HumanoidPequi/HumanoidPMec_LARC2023/Simulação/Martha_ws/src/martha_gazebo/src/worlds/robocup09_spl_field/thumbnails/4.png

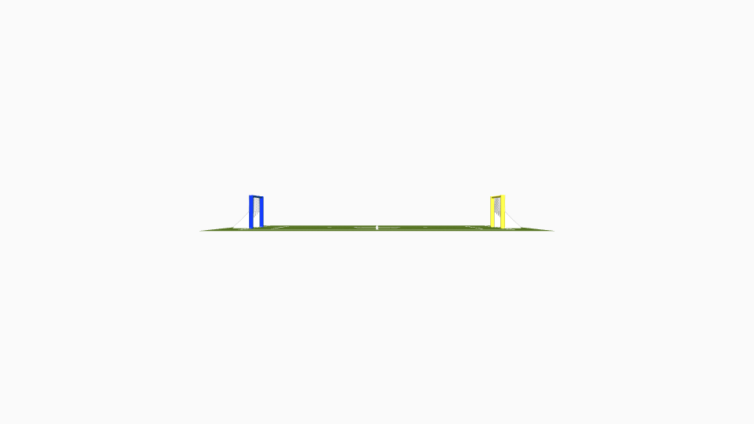
Simulação/Martha_ws/src/martha_gazebo/src/worlds/robocup09_spl_field/thumbnails/4.png
