HumanoidPequi/HumanoidPMec_LARC2023/Simulação/Martha_ws/src/martha_description/config/controller.yaml

martha:
  # Publish all joint states -----------------------------------
  joint_state_controller:
    type: joint_state_controller/JointStateController
    publish_rate: 50

  # Position Controllers --------------------------------------
  pescoco_rZ_position_controller:
    type: effort_controllers/JointPositionController
    joint: pescoco_rZ
    pid: {p: 10.0, i: 0.00000101, d: 0.11}

  cabeca_rX_position_controller:
    type: effort_controllers/JointPositionController
    joint: cabeca_rX
    pid: {p: 10.0, i: 0.00000101, d: 0.11}

  ombro_esquerdo_rX_position_controller:
    type: effort_controllers/JointPositionController
    joint: ombro_esquerdo_rX
    pid: {p: 10.0, i: 0.00000101, d: 0.11}
  ombro_esquerdo_rY_position_controller:
    type: effort_controllers/JointPositionController
    joint: ombro_esquerdo_rY
    pid: {p: 10.0, i: 0.00000101, d: 0.11}

  ombro_direito_rX_position_controller:
    type: effort_controllers/JointPositionController
    joint: ombro_direito_rX
    pid: {p: 10.0, i: 0.00000101, d: 0.11}
  ombro_direito_rY_position_controller:
    type: effort_controllers/JointPositionController
    joint: ombro_direito_rY
    pid: {p: 10.0, i: 0.00000101, d: 0.11}

  mao_esquerda_position_controller:
    type: effort_controllers/JointPositionController
    joint: mao_esquerda
    pid: {p: 1.0, i: 0.000001002, d: 0.002}
  mao_direita_position_controller:
    type: effort_controllers/JointPositionController
    joint: mao_direita
    pid: {p: 1.0, i: 0.000001002, d: 0.002}



  quadril_esquerdo_rX_position_controller:
    type: effort_controllers/JointPositionController
    joint: quadril_esquerdo_rX
    pid: {p: 40.0, i: 0.000001, d: 0.005}
  quadril_esquerdo_rY_position_controller:
    type: effort_controllers/JointPositionController
    joint: quadril_esquerdo_rY
    pid: {p: 40.0, i: 0.000001, d: 0.005}
  quadril_esquerdo_rZ_position_controller:
    type: effort_controllers/JointPositionController
    joint: quadril_esquerdo_rZ
    pid: {p: 40.0, i: 0.000001, d: 0.005}



  quadril_direito_rX_position_controller:
    type: effort_controllers/JointPositionController
    joint: quadril_direito_rX
    pid: {p: 40.0, i: 0.000001, d: 0.005}
  quadril_direito_rY_position_controller:
    type: effort_controllers/JointPositionController
    joint: quadril_direito_rY
    pid: {p: 40.0, i: 0.000001, d: 0.005}
  quadril_direito_rZ_position_controller:
    type: effort_controllers/JointPositionController
    joint: quadril_direito_rZ
    pid: {p: 40.0, i: 0.000001, d: 0.005}
  

  joelho_esquerdo_rX_position_controller:
    type: effort_controllers/JointPositionController
    joint: joelho_esquerdo_rX
    pid: {p: 40.0, i: 0.000001, d: 0.005}
  joelho_direito_rX_position_controller:
    type: effort_controllers/JointPositionController
    joint: joelho_direito_rX
    pid: {p: 40.0, i: 0.000001, d: 0.005}


  tornozelo_esquerdo_rX_position_controller:
    type: effort_controllers/JointPositionController
    joint: tornozelo_esquerdo_rX
    pid: {p: 40.0, i: 0.000001, d: 0.005}
  tornozelo_esquerdo_rY_position_controller:
    type: effort_controllers/JointPositionController
    joint: tornozelo_esquerdo_rY
    pid: {p: 40.0, i: 0.000001, d: 0.005}
  tornozelo_direito_rY_position_controller:
    type: effort_controllers/JointPositionController
    joint: tornozelo_direito_rY
    pid: {p: 40.0, i: 0.000001, d: 0.005}
  tornozelo_direito_rX_position_controller:
    type: effort_controllers/JointPositionController
    joint: tornozelo_direito_rX
    pid: {p: 40.0, i: 0.000001, d: 0.005} 
