HumanoidPequi/HumanoidPMec_LARC2023/Hardware/DynamixelArduino/Dynamixel_Servo_Example/Dynamixel_Servo_Example.ino

#include <Dynamixel_Servo.h>

#define HALF_DUPLEX_DIRECTION_PIN 2

/*--------------------------------------------------------------------*/
void setup(void)
{
  servo_init(&Serial, HALF_DUPLEX_DIRECTION_PIN, SERVO_DEFAULT_BAUD);
}

/*--------------------------------------------------------------------*/
void loop(void)
{
  int timeout = 50; //milliseconds
  servo_error_t error;
  
  /* using high-level interface */
  error = servo_set(SERVO_DEFAULT_ID, SERVO_REGISTER_GOAL_ANGLE, 0, timeout);
  //if(error) handle_error();
  delay(2000);
  
  error = servo_set(SERVO_DEFAULT_ID, SERVO_REGISTER_GOAL_ANGLE, 6.283, timeout);
  //if(error) handle_error();
  delay(2000);



  /* using low-level interface */
  /*  
  //int raw = servo_radians_to_raw(6.283);
  int raw = 4095;
  
  error = servo_set_raw_word(SERVO_DEFAULT_ID, SERVO_REGISTER_GOAL_ANGLE, 0, timeout);
  //if(error) handle_error();
  delay(2000);
    
  error = servo_set_raw_word(SERVO_DEFAULT_ID, SERVO_REGISTER_GOAL_ANGLE, raw, timeout);
  //if(error) handle_error();
  delay(2000);
  */
}
